amwales-888/TempGuard/Firmware/dsPIC33EV64GM004/GPIO.c

/* 
 *  Copyright (c) 2023 Angelo Masci
 * 
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
 */

#include <xc.h>
#include <stdint.h>

#include "mcc_generated_files/pin_manager.h"
#include "GPIO.h"

void
GPIOEnablePullDown(uint16_t id) {

    switch (id) {
        case 0:
            CNPDA |= (1 << 0); // Enable Pull-down A0
            return;
        case 1:
            CNPDA |= (1 << 1); // Enable Pull-down A1
            return;
        case 2:
            CNPDA |= (1 << 9); // Enable Pull-down A9
            return;
        case 3:
            CNPDC |= (1 << 0); // Enable Pull-down C0
            return;
        case 4:
            CNPDC |= (1 << 1); // Enable Pull-down C1
            return;
        case 5:
            CNPDC |= (1 << 2); // Enable Pull-down C2
            return;
    }
}

void
GPIOEnablePullUp(uint16_t id) {

    switch (id) {
        case 0:
            CNPUA |= (1 << 0); // Enable Pull-up A0
            return;
        case 1:
            CNPUA |= (1 << 1); // Enable Pull-up A1
            return;
        case 2:
            CNPUA |= (1 << 9); // Enable Pull-up A9
            return;
        case 3:
            CNPUC |= (1 << 0); // Enable Pull-up C0
            return;
        case 4:
            CNPUC |= (1 << 1); // Enable Pull-up C1
            return;
        case 5:
            CNPUC |= (1 << 2); // Enable Pull-up C2
            return;
    }
}

void
GPIODisablePullDown(uint16_t id) {
    
    switch (id) {
        case 0:
            CNPDA &= ~(1 << 0); // Disable Pull-down A0
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
            case 3:
                GPIO3_SetDigitalInput();
                return; 
            case 4:
                GPIO4_SetDigitalInput();
                return; 
            case 5:
                GPIO5_SetDigitalInput();
                return; 
        }        
    }
}

void
GPIOSetType(uint16_t id, enum GPIOType type) {
        
    switch (id) {
        case 0:
            ANSELAbits.ANSA0 = type;
            return;
        case 1:
            ANSELAbits.ANSA1 = type;
            return;
        case 2:
            ANSELAbits.ANSA9 = type;
            return;
        case 3:
            ANSELCbits.ANSC0 = type;
            return;
        case 4:
            ANSELCbits.ANSC1 = type;
            return;
        case 5:
            ANSELCbits.ANSC2 = type;
            return;
    }            
}
