amwales-888/TempGuard/Firmware/dsPIC33EV64GM004/format.c

/* 
 *  Copyright (c) 2023 Angelo Masci
 * 
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
 */

#include <stdint.h>

#include "format.h"

void 
formatNumber2Right(char *ptr, uint16_t n) {
    
    // Convert uint value to string ##
    
    if (n < 0) {
        
        *ptr++ = 'L';
        *ptr++ = 'O';

    } else if (n > 99) {
        
        *ptr++ = 'H';
        *ptr++ = 'I';

    } else {

        if (n < 10) {
                        
            ptr += 1; 
            
            *ptr-- = '0' + (n % 10);        
            *ptr   = ' ';
            
        } else if (n < 100) {
            
            ptr += 1; 

            *ptr-- = '0' + (n % 10);
            n /= 10;
            *ptr   = '0' + (n % 10);
        }        
    }
}

void 
formatNumber2(char *ptr, uint16_t n) {
    
    // Convert uint value to string ##
    
    if (n < 0) {
        
        *ptr++ = 'L';
        *ptr++ = 'O';

    } else if (n > 99) {
        
        *ptr++ = 'H';
        *ptr++ = 'I';

    } else {

        if (n < 10) {
                        
            ptr += 1; 
            
            *ptr-- = '0' + (n % 10);        
            *ptr   = '0';
            
        } else if (n < 100) {
            
            ptr += 1; 

            *ptr-- = '0' + (n % 10);
            n /= 10;
            *ptr   = '0' + (n % 10);
        }        
    }
}






void 
formatNumberRight(char *ptr, uint16_t n) {
    
    // Convert uint value to string ###
    
    if (n < 0) {
        
        *ptr++ = 'L';
        *ptr++ = 'O';
        *ptr   = ' ';

    } else if (n > 999) {
        
        *ptr++ = 'H';
        *ptr++ = 'I';
        *ptr   = ' ';

    } else {

        if (n < 10) {
                        
            ptr += 2; 
            
            *ptr-- = '0' + (n % 10);        
            *ptr-- = ' ';
            *ptr   = ' ';
            
        } else if (n < 100) {
            
            ptr += 2; 

            *ptr-- = '0' + (n % 10);
            n /= 10;
            *ptr-- = '0' + (n % 10);
            *ptr   = ' ';

        } else if (n < 1000) {
            
            ptr += 2; 

            *ptr-- = '0' + (n % 10);
            n /= 10;
            *ptr-- = '0' + (n % 10);
            n /= 10;
            *ptr   = '0' + (n % 10);
        }        
    }
}

void 
formatRPM(char *ptr, uint16_t n) {
    
    // Convert uint value to string ####
    
    if (n < 0) {
        
        *ptr++ = 'L';
        *ptr++ = 'O';
        *ptr++ = ' ';
        *ptr   = ' ';

    } else if (n > 9999) {
        
        *ptr++ = 'H';
        *ptr++ = 'I';
        *ptr++ = ' ';
        *ptr   = ' ';

    } else {

        ptr += 3; 
        
        *ptr-- = '0' + (n % 10);        
        n /= 10;
        *ptr-- = '0' + (n % 10);        
        n /= 10;
        *ptr-- = '0' + (n % 10);
        n /= 10;
        *ptr = '0' + (n % 10);
        
        // remove leading zeros

        if (*ptr == '0') *ptr++ = ' ';
        if (*ptr == '0') *ptr++ = ' ';
        if (*ptr == '0') *ptr++ = ' ';
    }
}

void 
formatNumber(char *ptr, uint16_t n) {
    
    // Convert uint value to string ###
    
    if (n < 0) {
        
        *ptr++ = 'L';
        *ptr++ = 'O';
        *ptr   = ' ';

    } else if (n > 100) {
        
        *ptr++ = 'H';
        *ptr++ = 'I';
        *ptr   = ' ';

    } else {

        ptr += 2; 
        
        *ptr-- = '0' + (n % 10);        
        n /= 10;
        *ptr-- = '0' + (n % 10);
        n /= 10;
        *ptr = '0' + (n % 10);
        
        // remove leading zeros

        if (*ptr == '0') *ptr++ = ' ';
        if (*ptr == '0') *ptr++ = ' ';
    }
}


void 
formatTemp(char *ptr, double v) {

    /* Convert double value to string ##.# */

    if (v < 0) {
        
        *ptr++ = 'L';
        *ptr++ = 'O';
        *ptr++ = ' ';
        *ptr   = ' ';

    } else if (v < 100) {
        
        int n = (int)v;
        int f = (v - n) * 10;

        ptr += 3; 
        
        *ptr-- = '0' + f;
        *ptr-- = '.';
        *ptr-- = '0' + (n % 10);
        
        n /= 10;
        if (n > 0) {
            *ptr = '0' + (n % 10);
        } else {
            *ptr = ' ';
        }
        
    } else {
        
        *ptr++ = 'H';
        *ptr++ = 'I';
        *ptr++ = ' ';
        *ptr   = ' ';
    }
}
